jabadiagm/MSXgoauldSD_tn20k/fpga/G80A/g80a.vhd

--
-- Z80 compatible microprocessor core, asynchronous top level
--
-- Version : 0250_T80 (+k04)
--
-- Copyright (c) 2001-2002 Daniel Wallner (jesus@opencores.org)
--
-- All rights reserved
--
-- Redistribution and use in source and synthezised forms, with or without
-- modification, are permitted provided that the following conditions are met:
--
-- Redistributions of source code must retain the above copyright notice,
-- this list of conditions and the following disclaimer.
--
-- Redistributions in synthesized form must reproduce the above copyright
-- notice, this list of conditions and the following disclaimer in the
-- documentation and/or other materials provided with the distribution.
--
-- Neither the name of the author nor the names of other contributors may
-- be used to endorse or promote products derived from this software without
-- specific prior written permission.
--
-- THIS SOFTWARE IS PROVIDED BY THE COPYRIGHT HOLDERS AND CONTRIBUTORS "AS IS"
-- AND ANY EXPRESS OR IMPLIED WARRANTIES, INCLUDING, BUT NOT LIMITED TO,
-- THE IMPLIED WARRANTIES OF MERCHANTABILITY AND FITNESS FOR A PARTICULAR
-- PURPOSE ARE DISCLAIMED. IN NO EVENT SHALL THE AUTHOR OR CONTRIBUTORS BE
-- LIABLE FOR ANY DIRECT, INDIRECT, INCIDENTAL, SPECIAL, EXEMPLARY, OR
-- CONSEQUENTIAL DAMAGES (INCLUDING, BUT NOT LIMITED TO, PROCUREMENT OF
-- SUBSTITUTE GOODS OR SERVICES; LOSS OF USE, DATA, OR PROFITS; OR BUSINESS
-- INTERRUPTION) HOWEVER CAUSED AND ON ANY THEORY OF LIABILITY, WHETHER IN
-- CONTRACT, STRICT LIABILITY, OR TORT (INCLUDING NEGLIGENCE OR OTHERWISE)
-- ARISING IN ANY WAY OUT OF THE USE OF THIS SOFTWARE, EVEN IF ADVISED OF THE
-- POSSIBILITY OF SUCH DAMAGE.
--
-- Please report bugs to the author, but before you do so, please
-- make sure that this is not a derivative work and that
-- you have the latest version of this file.
--
-- The latest version of this file can be found at:
--  http://www.opencores.org/cvsweb.shtml/t80/
--
-- Limitations :
--
-- File history :
--
--  0208 : First complete release
--  0211 : Fixed interrupt cycle
--  0235 : Updated for T80 interface change
--  0238 : Updated for T80 interface change
--  0240 : Updated for T80 interface change
--  0242 : Updated for T80 interface change
--  0247 : Fixed bus req/ack cycle
--  0247a: 7th of September, 2003 by Kazuhiro Tsujikawa (tujikawa@hat.hi-ho.ne.jp)
--         Fixed IORQ_n, RD_n, WR_n bus timing
--  0250 : Added R800 Multiplier by TobiFlex 2017.10.15
--
--  +k01 : Added RstKeyLock and swioRESET_n by KdL 2010.10.25
--  +k02 : Added R800_mode signal by KdL 2018.05.14
--  +k03 : RstKeyLock and swioRESET_n were put back outside of T80 by KdL 2019.05.20
--  +k04 : Separation of T800 from T80 by KdL 2021.02.01
--

library IEEE;
use IEEE.std_logic_1164.all;
use IEEE.numeric_std.all;
use work.T80_Pack.all;

entity G80a is
    generic(
        Mode        : integer := 0;     -- 0 => Z80, 1 => Fast Z80, 2 => 8080, 3 => GB
        IOWait      : integer := 1      -- 0 => Single I/O cycle, 1 => Std I/O cycle
    );
    port(
        RESET_n     : in std_logic;
        CLK_n       : in std_logic;
		clk_enable  : in std_logic;
		clk_falling	: in std_logic;
        WAIT_n      : in std_logic;
        INT_n       : in std_logic;
        NMI_n       : in std_logic;
        BUSRQ_n     : in std_logic;
        M1_n        : out std_logic;
        MREQ_n      : out std_logic;
        IORQ_n      : out std_logic;
        RD_n        : out std_logic;
        WR_n        : out std_logic;
        RFSH_n      : out std_logic;
        HALT_n      : out std_logic;
        BUSAK_n     : out std_logic;
        A           : out std_logic_vector(15 downto 0);
		update_addr	: out std_logic;
        DI           : in std_logic_vector(7 downto 0);
        DO           : out std_logic_vector(7 downto 0);
        Data_Reverse: out std_logic
    );
end G80a;

architecture rtl of G80a is

    signal CEN          : std_logic;
    signal Reset_s      : std_logic;
    signal IntCycle_n   : std_logic;
    signal IORQ         : std_logic;
    signal NoRead       : std_logic;
    signal Write        : std_logic;
    signal MREQ         : std_logic;
    signal MReq_Inhibit : std_logic;
    signal IReq_Inhibit : std_logic;        -- 0247a
    signal Req_Inhibit  : std_logic;
    signal RD           : std_logic;
    signal MREQ_n_i     : std_logic;
    signal IORQ_n_i     : std_logic;
    signal RD_n_i       : std_logic;
    signal WR_n_i       : std_logic;
    signal WR_n_j       : std_logic;        -- 0247a
    signal RFSH_n_i     : std_logic;
    signal BUSAK_n_i    : std_logic;
    signal A_i          : std_logic_vector(15 downto 0);
    signal A_prev       : std_logic_vector(15 downto 0);    -- direccion del ciclo anterior (deteccion de cambio real)
    signal update_addr_i: std_logic;                        -- update_addr crudo del core T80
    --signal DO           : std_logic_vector(7 downto 0);
    signal DI_Reg       : std_logic_vector (7 downto 0);    -- Input synchroniser
    signal Wait_s       : std_logic;
    signal MCycle       : std_logic_vector(2 downto 0);
    signal TState       : std_logic_vector(2 downto 0);

begin

	--CEN <= '1';
    CEN <= clk_enable;

    BUSAK_n <= BUSAK_n_i;
    MREQ_n_i <= not MREQ or (Req_Inhibit and MReq_Inhibit);
    RD_n_i <= not RD or Req_Inhibit;
    WR_n_j <= WR_n_i;                                                   -- 0247a

    MREQ_n <= MREQ_n_i when BUSAK_n_i = '1' else 'Z';
    IORQ_n <= IORQ_n_i or IReq_Inhibit when BUSAK_n_i = '1' else 'Z';   -- 0247a
    RD_n <= RD_n_i when BUSAK_n_i = '1' else 'Z';
    WR_n <= WR_n_j when BUSAK_n_i = '1' else 'Z';                       -- 0247a
    RFSH_n <= RFSH_n_i when BUSAK_n_i = '1' else 'Z';
    A <= A_i when BUSAK_n_i = '1' else (others => 'Z');
    --D <= DO when Write = '1' and BUSAK_n_i = '1' else (others => 'Z');
    Data_Reverse <= Write;

    -- update_addr solo cuando la direccion realmente cambia de valor.
    -- Es un subconjunto del pulso crudo del core: solo puede suprimir pulsos
    -- espurios (recargas de A con el mismo valor), nunca crear nuevos.
    -- REGISTRADO en clk_54m: (a) mantiene el comparador de 16 bits en una ruta
    -- 54->54 (periodo completo) en vez de meterlo en la ruta cross-domain hacia
    -- state_demux (clk_108m), (b) restaura la naturaleza registrada del update_addr
    -- original. La latencia de 1 ciclo de 54 MHz es inocua: es un nivel ancho
    -- (~15 ciclos) y la direccion ya esta estable en el bus.
    process (Reset_s, CLK_n)
    begin
        if Reset_s = '0' then
            update_addr <= '0';
        elsif CLK_n'event and CLK_n = '1' then
            if A_i /= A_prev then
                update_addr <= update_addr_i;
            else
                update_addr <= '0';
            end if;
        end if;
    end process;

    -- Snapshot de A_i con la misma cadencia que el core (flanco subida + clk_enable).
    -- Tras el flanco: A_i = direccion nueva, A_prev = la anterior.
    process (Reset_s, CLK_n)
    begin
        if Reset_s = '0' then
            A_prev <= (others => '1');   -- distinto del A de reset (0): no pierde el primer cambio
        elsif CLK_n'event and CLK_n = '1' then
            if clk_enable = '1' then
                A_prev <= A_i;
            end if;
        end if;
    end process;

    process (RESET_n, CLK_n)
    begin
        if RESET_n = '0' then
            Reset_s <= '0';
        elsif CLK_n'event and CLK_n = '1' then
			if clk_enable = '1' then
				Reset_s <= '1';
			end if;
        end if;
    end process;

    u0 : T80
        generic map(
            Mode => Mode,
            IOWait => IOWait)
        port map(
            CEN => CEN,
            M1_n => M1_n,
            IORQ => IORQ,
            NoRead => NoRead,
            Write => Write,
            RFSH_n => RFSH_n_i,
            HALT_n => HALT_n,
            WAIT_n => Wait_s,
            INT_n => INT_n,
            NMI_n => NMI_n,
            RESET_n => Reset_s,
            BUSRQ_n => BUSRQ_n,
            BUSAK_n => BUSAK_n_i,
            CLK_n => CLK_n,
            A => A_i,
			update_addr => update_addr_i,
            DInst => DI,
            DI => DI_Reg,
            DO => DO,
            MC => MCycle,
            TS => TState,
            IntCycle_n => IntCycle_n);

    process (CLK_n)
    begin
        if CLK_n'event and CLK_n = '0' then
            Wait_s <= WAIT_n;
			if clk_falling = '1' then
				if TState = "011" and BUSAK_n_i = '1' then
					DI_Reg <= to_x01(DI);
				end if;
			end if;
        end if;
    end process;

    process (CLK_n)                         -- 0247a
    begin
        if CLK_n'event and CLK_n = '1' then
			if clk_enable = '1' then
				IReq_Inhibit <= not IORQ;
			end if;
        end if;
    end process;

    process (Reset_s,CLK_n)                 -- 0247a
    begin
        if Reset_s = '0' then
            WR_n_i <= '1';
        elsif CLK_n'event and CLK_n = '0' then
			if clk_falling = '1' then
				if (IORQ = '0') then
					if TState = "010" then
						WR_n_i <= not Write;
					elsif Tstate = "011" then
						WR_n_i <= '1';
					end if;
				else
					if TState = "001" and IORQ_n_i = '0' then
						WR_n_i <= not Write;
					elsif Tstate = "011" then
						WR_n_i <= '1';
					end if;
				end if;
			end if;
        end if;
    end process;

    process (Reset_s,CLK_n)                 -- 0247a
    begin
        if Reset_s = '0' then
            Req_Inhibit <= '0';
        elsif CLK_n'event and CLK_n = '1' then
			if clk_enable = '1' then
				if MCycle = "001" and TState = "010" and wait_s = '1' then
					Req_Inhibit <= '1';
				else
					Req_Inhibit <= '0';
				end if;
			end if;
        end if;
    end process;

    process (Reset_s,CLK_n)
    begin
        if Reset_s = '0' then
            MReq_Inhibit <= '0';
        elsif CLK_n'event and CLK_n = '0' then
			if clk_falling = '1' then
				if MCycle = "001" and TState = "010" then
					MReq_Inhibit <= '1';
				else
					MReq_Inhibit <= '0';
				end if;
			end if;
        end if;
    end process;

    process (Reset_s,CLK_n)                 -- 0247a
    begin
        if Reset_s = '0' then
            RD <= '0';
            IORQ_n_i <= '1';
            MREQ <= '0';
        elsif CLK_n'event and CLK_n = '0' then
			if clk_falling = '1' then
				if MCycle = "001" then
					if TState = "001" then
						RD <= IntCycle_n;
						MREQ <= IntCycle_n;
						IORQ_n_i <= IntCycle_n;
					end if;
					if TState = "011" then
						RD <= '0';
						IORQ_n_i <= '1';
						MREQ <= '1';
					end if;
					if TState = "100" then
						MREQ <= '0';
					end if;
				else
					if TState = "001" and NoRead = '0' then
						IORQ_n_i <= not IORQ;
						MREQ <= not IORQ;
						if IORQ = '0' then
						  RD <= not Write;
						elsif IORQ_n_i = '0' then
						  RD <= not Write;
						end if;
					end if;
					if TState = "011" then
						RD <= '0';
						IORQ_n_i <= '1';
						MREQ <= '0';
					end if;
				end if;
			end if;
        end if;
    end process;

end;
