jabadiagm/MSXgoauldSD_tn20k/fpga/vdp/vdp_hvcounter.v

//
//  vdp_hvcounter.v
//   Horizontal / vertical counters, field ID, H/V blanking, HDMI reset on mode change.
//   Traduccion a Verilog de vdp_hvcounter.vhd.
//
//  Copyright (C) Kunihiko Ohnaka / ESE-VDP contributors.
//  Licencia completa (redistribucion / disclaimer) en el original vdp_hvcounter.vhd.
//
//  NOTA (traduccion): en el original CLOCKS_PER_LINE/HALF eran SHARED VARIABLE que
//   hvcounter reasignaba segun PAL (1728/864). Aqui se calculan como wire local a
//   partir de PAL_MODE (mismo valor en estado estable). Los otros modulos acoplados
//   (ssg/ntsc_pal/vga/vdp) hacen lo mismo con su propia señal PAL -> todos coherentes.
//-----------------------------------------------------------------------------

module VDP_HVCOUNTER (
    input  wire        RESET,
    input  wire        CLK21M,

    output wire [10:0] H_CNT,
    output wire [10:0] H_CNT_IN_FIELD,
    output wire [ 9:0] V_CNT_IN_FIELD,
    output wire [10:0] V_CNT_IN_FRAME,
    output wire        FIELD,
    output wire        H_BLANK,
    output wire        V_BLANK,

    input  wire        PAL_MODE,
    input  wire        INTERLACE_MODE,
    input  wire        Y212_MODE,
    input  wire [ 6:0] OFFSET_Y,
    output wire        HDMI_RESET,
    input  wire        BLANKING_START,
    input  wire        BLANKING_END
);

`include "vdp_package.vh"

    // CLOCKS por linea, dependientes de PAL (antes SHARED VARIABLE mutado aqui)
    wire [11:0] CLOCKS_PER_LINE      = (PAL_MODE == 1'b1) ? 12'd1728 : 12'd1716;
    wire [11:0] CLOCKS_PER_HALF_LINE = (PAL_MODE == 1'b1) ? 12'd864  : 12'd858;

    // FLIP FLOP
    reg [10:0] FF_H_CNT;
    reg [10:0] FF_H_CNT_IN_FIELD;
    reg [ 9:0] FF_V_CNT_IN_FIELD;
    reg        FF_FIELD;
    reg [10:0] FF_V_CNT_IN_FRAME;
    reg        FF_H_BLANK;
    reg        FF_V_BLANK;
    reg        FF_PAL_MODE;
    reg        FF_INTERLACE_MODE;
    reg        FF_FIELD_END;
    reg        FF_HDMI_RESET;

    // WIRE
    wire       W_H_CNT_HALF;
    wire       W_H_CNT_END;
    wire       W_FIELD_END;
    wire       W_H_BLANK_START;
    wire       W_H_BLANK_END;
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
